NCKiser/OOPS--All-Knobs/USB_Reset_Flash.png

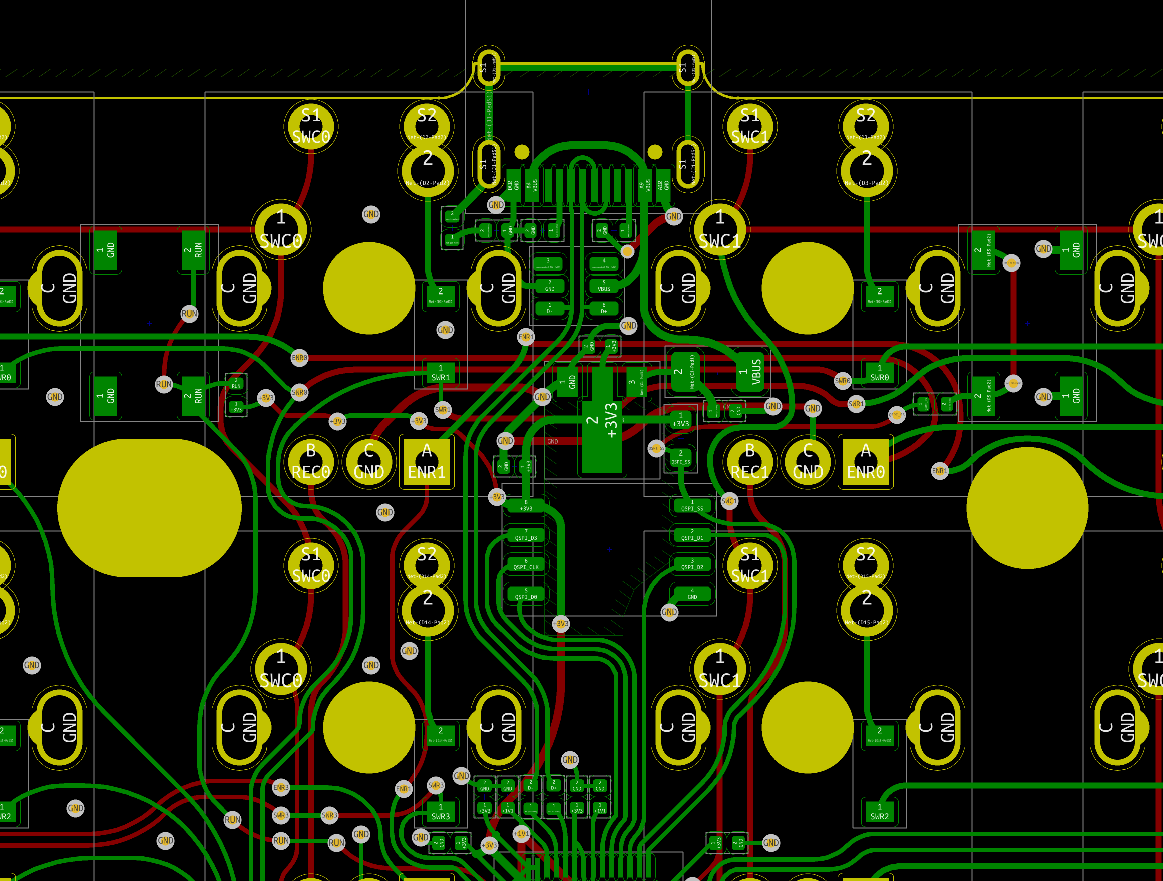
USB_Reset_Flash.png
